Outdatedcandy92/RP2040-DBUG-Probe/attachments/A.png

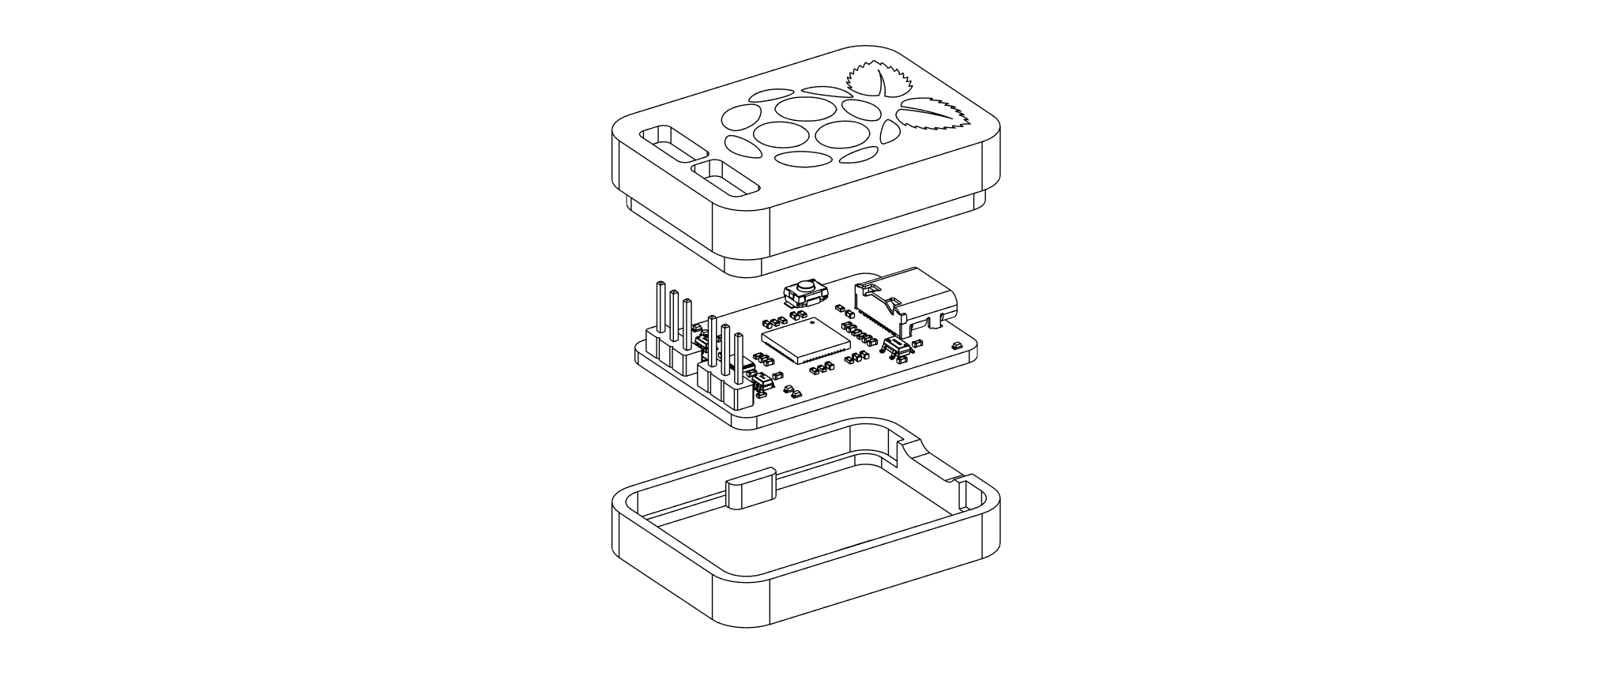
attachments/A.png
