Outdatedcandy92/RP2040-DBUG-Probe/attachments/Fusion360_6LrPjNnVSa.png

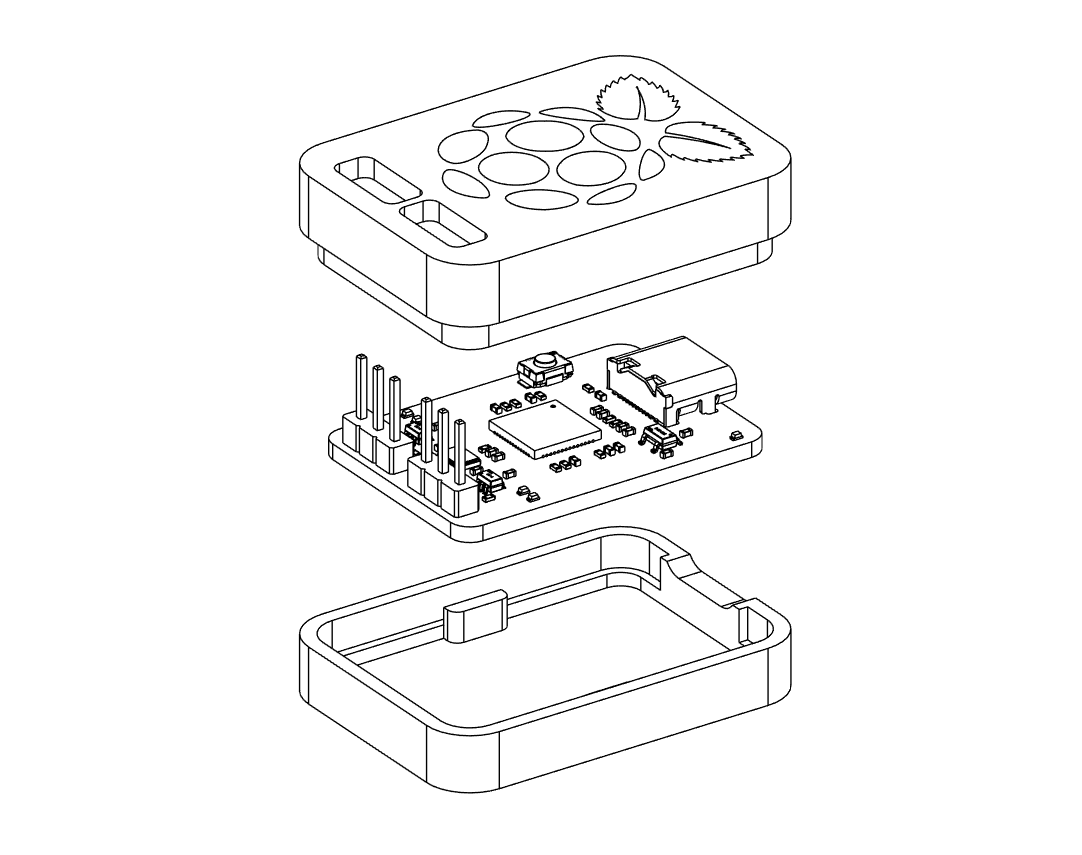
attachments/Fusion360_6LrPjNnVSa.png
