Outdatedcandy92/RP2040-DBUG-Probe/attachments/Fusion360_ywjbid8xCV.png

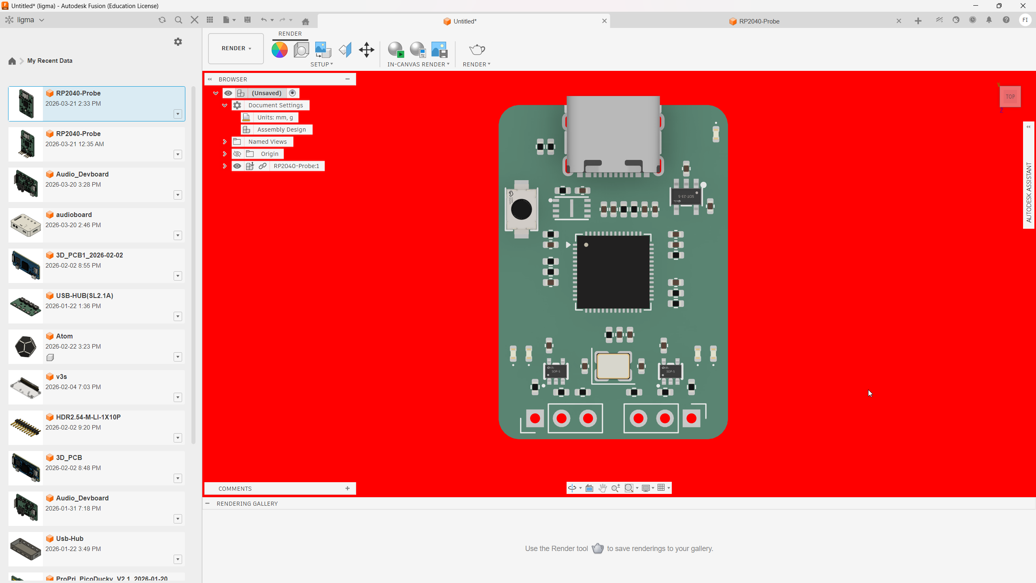
attachments/Fusion360_ywjbid8xCV.png
