Outdatedcandy92/RP2040-DBUG-Probe/attachments/kicad_7gLrpzjUqe.png

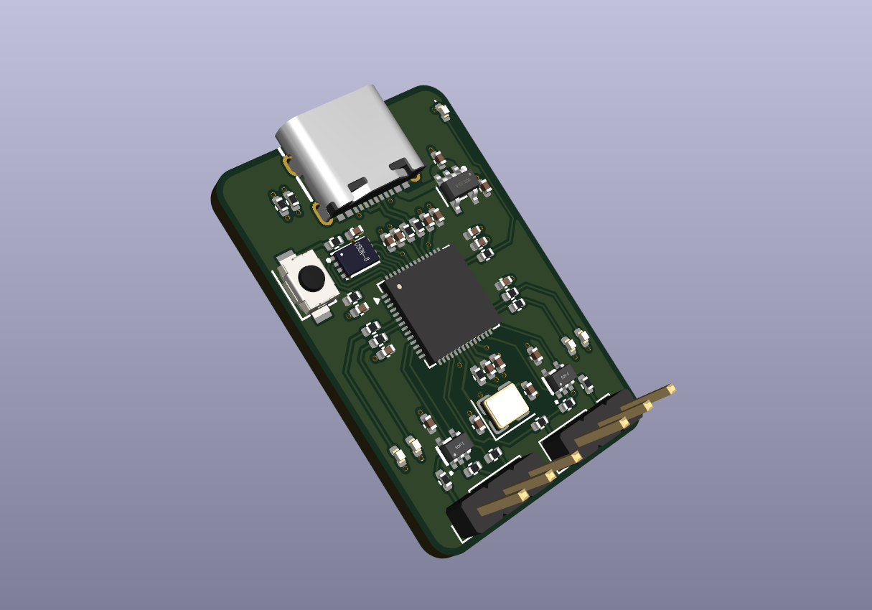
attachments/kicad_7gLrpzjUqe.png
