Outdatedcandy92/RP2040-DBUG-Probe/attachments/Pasted image 20251225222923.png

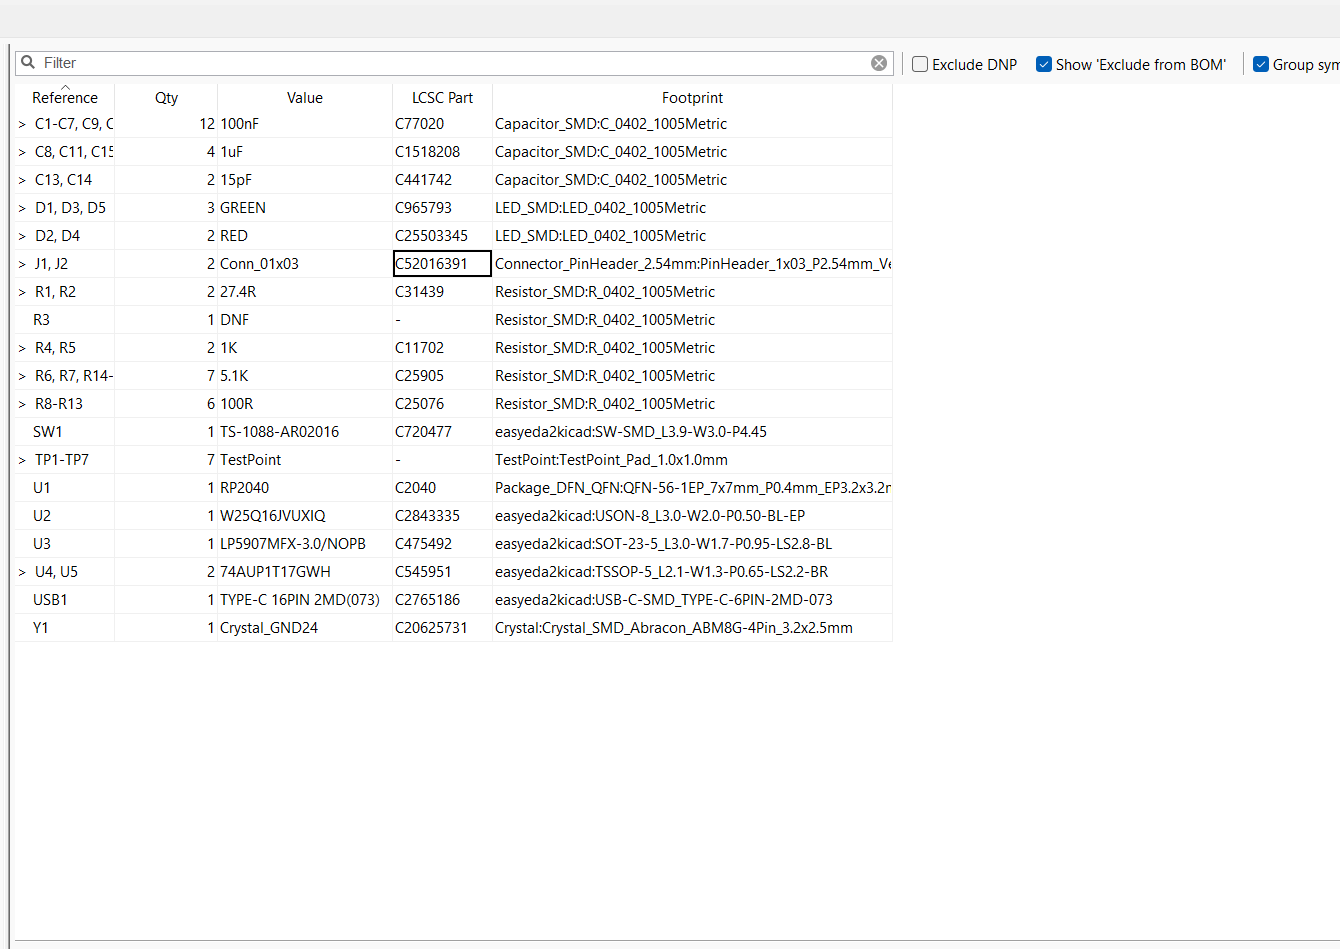
attachments/Pasted image 20251225222923.png
