Outdatedcandy92/RP2040-DBUG-Probe/attachments/Screenshot 2025-12-25 195522.png

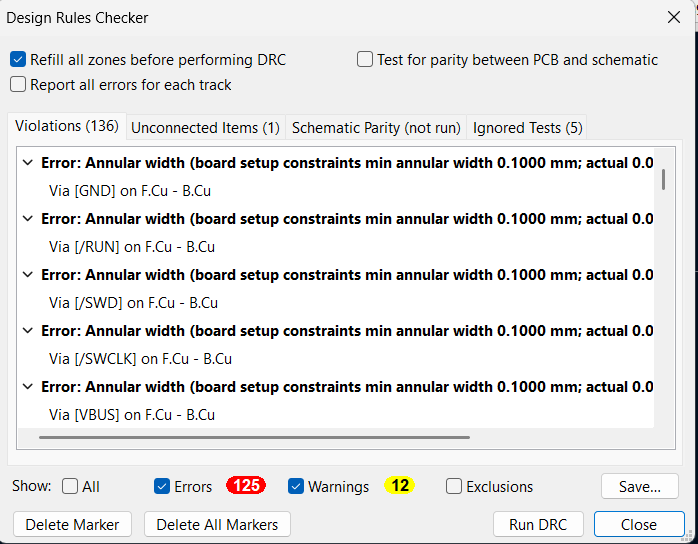
attachments/Screenshot 2025-12-25 195522.png
